myriadrf/LimeSDR-Mini/hardware/1v0/Project Outputs for LimeSDR_Mini_1v0/ERC/LimeSDR_Mini_1v0.html

Altium

# Electrical Rule Check Report

Date: | | 2017-09-22
Time: | | 12:20:39
Filename: | | D:\Aleksandr\Desktop\LimeSDR_Mini_1v0_Rounded_DFMr1\Project Outputs for LimeSDR_Mini_1v0\ERC\LimeSDR_Mini_1v0.html

Class | Document | Message
Warning | 09_Misc.SchDoc | GND contains IO Pin and Power Pin objects (Pin IC9-5,Pin IC5-E3,Pin IC5-E4,Pin IC5-F4,Pin IC5-G4)
Warning | 09_Misc.SchDoc | Net NetC151_2 has no driving source (Pin C151-2,Pin XO1-7)
Warning | 07_FPGA.SchDoc | Net NetIC5_E7 has no driving source (Pin IC5-E7,Pin R47-2)
Warning | 09_Misc.SchDoc | Net NetIC14_5 has no driving source (Pin IC14-5,Pin R80-1,Pin R81-1)
Warning | 09_Misc.SchDoc | Net TCXO_VC has no driving source (Pin C161-2,Pin R67-1,Pin R68-1,Pin XO1-1)
Warning | 08_USB3_0_device.SchDoc | Net USB_SSRX_N has no driving source (Pin ESD3-7,Pin IC6-34,Pin J7-8)
Warning | 08_USB3_0_device.SchDoc | Net USB_SSRX_P has no driving source (Pin ESD3-8,Pin IC6-35,Pin J7-9)

Back to top
